et0614/e-sensor/firmware/E_Sensor_Main.X/main.c

#include "mcc_generated_files/system/system.h"
#include "mcc_generated_files/system/ccp.h"
#include "mcc_generated_files/timer/tca0.h"
#include "mcc_generated_files/system/pins.h"

#include <avr/interrupt.h>
#include <avr/wdt.h>
#include <avr/sleep.h>

#include "tinyusb/tusb.h"
#include "midi_app.h"
#include "opt3001.h"
#include "velocity_sensor.h"
#include "stcc4.h"
#include "eeprom_manager.h"

#include <util/atomic.h>

volatile uint32_t system_millis = 0;
volatile uint32_t sec_timer = 0;
// CO2 初期調整用のタイマ。休眠状態は -1、調整要求受信時に 0 にセットされ、
// ISR が 0 以上の場合のみ 1msec 刻みでインクリメントする。起動直後に
// CMD_CONDITIONING_DONE が誤発火しないよう -1 で初期化する。
volatile int32_t co2_pfm_timer = -1;

volatile bool conditioning_requested = false;

// 1msecごとのコールバック関数
void msecHandler(void)
{
    // ISR内なので他割り込みによる競合は無い。単純インクリメントでよい。
    system_millis++;
    sec_timer++;
    if(0 <= co2_pfm_timer) co2_pfm_timer++;
}

// 32bit変数をアトミックに読むヘルパ
static inline uint32_t atomic_load_u32(volatile uint32_t *p) {
    uint32_t v;
    ATOMIC_BLOCK(ATOMIC_RESTORESTATE) { v = *p; }
    return v;
}
static inline int32_t atomic_load_i32(volatile int32_t *p) {
    int32_t v;
    ATOMIC_BLOCK(ATOMIC_RESTORESTATE) { v = *p; }
    return v;
}
static inline void atomic_store_u32(volatile uint32_t *p, uint32_t v) {
    ATOMIC_BLOCK(ATOMIC_RESTORESTATE) { *p = v; }
}
static inline void atomic_store_i32(volatile int32_t *p, int32_t v) {
    ATOMIC_BLOCK(ATOMIC_RESTORESTATE) { *p = v; }
}

// TinyUSBが参照する時間取得関数をオーバーライド
uint32_t tusb_time_millis_api(void) {
    uint32_t now;
    ATOMIC_BLOCK(ATOMIC_RESTORESTATE) {
        now = system_millis;
    }
    return now;
}

void setup_usb(void) {
    // 1. 周波数を 12MHz に設定 (USB FS の下限。Microchip 公式 CDC 例より、AVR DU の
    //    USB フルスピード動作に必要な最低オシレータ周波数は 12MHz。24MHz から半減させ、
    //    発振器・常時動作周辺（USB/TCA0/I2C）の動的消費＝自己発熱を更に低減する。
    //    ※USB の下限が 12MHz なので、USB 接続中はこれ以上は下げられない。
    // 2. AUTOTUNE を SOF (USB Start of Frame) に同期する設定にする（12MHz でも SOF 同期は有効）
    ccp_write_io((void *)&(CLKCTRL.OSCHFCTRLA), CLKCTRL_FRQSEL_12M_gc | CLKCTRL_AUTOTUNE_SOF_gc);
    
    SYSCFG.VUSBCTRL = SYSCFG_USBVREG_bm;
    
     //Tiny USB初期化
     tusb_init();
     
     // PCに対してUSB接続を通知
    USB0.CTRLB |= USB_ATTACH_bm;
}

int main(void)
{
    SYSTEM_Initialize();

    // EEPROM読み込み
    EM_loadEEPROM();
    
    // センサ初期化
    STCC4_initialize();
    OPT3001_Initialize();
    VELS_stop(); // 起動時は風速計OFF（5V遮断）を明示。On はホストからの指令で行う
    
    // STCC4は初回起動時のみ工場出荷状態に初期化
    if(EM_Is_First_Run)
    {
        if(STCC4_performFactoryReset())
        {
            //成功したらフラグ解除。失敗の場合は次回起動時に持ち越す
            EM_Is_First_Run = false;
            EM_updateEEPROM();
        }
    }
    STCC4_exitSleep();
    STCC4_startContinuousMeasurement(); //CO2連続計測開始
    
    MIDI_APP_Initialize();
    
    // イベントハンドラ登録
    TCA0_OverflowCallbackRegister(msecHandler); // 1msecタイマ
    
    // USB通信用意
    setup_usb();

    // 割り込み開始
    sei();

    B_LED_SetLow();

    // スリープモードは IDLE。CPU コアのみ停止し、USB・TCA0(1ms)・I2C 等の周辺は
    // 動作を継続する。割込（USB 転送/SOF、1ms タイマ等）で即復帰してループを回す。
    // これにより常時クロックでビジーループしていた分の動的消費（=自己発熱）を抑える。
    // ※STANDBY/POWER-DOWN は USB クロックも停止し接続が切れるため使用不可。
    set_sleep_mode(SLEEP_MODE_IDLE);

    while(1)
    {
        // ウォッチドッグキック
        wdt_reset();

        tud_task();         // USBスタック
        MIDI_APP_Tasks();   // MIDIアプリ処理

        // CO2センサ初期調整関連
        if(conditioning_requested && STCC4_performConditioning())
        {
            conditioning_requested = false;
            MIDI_SendSysEx(CMD_CONDITIONING_START, NULL, 0);
            atomic_store_i32(&co2_pfm_timer, 0);
        }
        // 初期調整（約22sec）が終わったらCO2センサの連続計測開始
        if(23000 < atomic_load_i32(&co2_pfm_timer))
        {
            if(STCC4_startContinuousMeasurement())
            {
                MIDI_SendSysEx(CMD_CONDITIONING_DONE, NULL, 0);
                atomic_store_i32(&co2_pfm_timer, -1);
            }
            else
            {
                // 失敗時は I2C を叩き続けないよう 1sec バックオフして再試行
                atomic_store_i32(&co2_pfm_timer, 22000);
            }
        }

        // 1secタイマ
        if(1000 < atomic_load_u32(&sec_timer))
        {
            atomic_store_u32(&sec_timer, 0);

            if(EM_Sensing_Enabled) B_LED_Toggle();
            else B_LED_SetLow();
        }

        // 次の割込まで CPU を休止（IDLE）。USB 割込・1ms タイマ等で復帰する。
        // 遅くとも 1ms ごとに TCA0 で起床するため処理の取りこぼしは生じない。
        sleep_mode();
    }
}
