et0614/e-sensor/firmware/E_Sensor_Main.X/midi_app.c

#include "midi_app.h"
#include "sensor_data.h"
#include "crc.h"
#include "tinyusb/tusb.h"

#include <string.h>
#include <util/atomic.h>

#include "opt3001.h"
#include "stcc4.h"
#include "velocity_sensor.h"
//#include "smAverage.h" //平均化ユーティリティ
#include "serial.h"
#include "eeprom_manager.h"

// バージョン
#define VERSION_MAJOR (1)
#define VERSION_MINOR (1)
#define VERSION_REVISION (2)

// 計測時間間隔 [msec]
#define MEAS_CO2_SPAN (1000)
#define MEAS_ILL_SPAN (800)
#define MEAS_VEL_SPAN (200)

#define SYSEX_BUF_SIZE 64
static uint8_t rx_buf[SYSEX_BUF_SIZE];
static uint16_t rx_idx = 0;

// SysEx受信の状態機械
typedef enum {
    SYSEX_IDLE,      // 0xF0 待ち
    SYSEX_RX,        // ペイロード蓄積中
    SYSEX_OVERFLOW   // バッファ溢れ: 0xF7 までデータを破棄
} sysex_rx_state_t;

static sysex_rx_state_t rx_state = SYSEX_IDLE;

static inline void sysex_reset_rx(void) {
    rx_idx = 0;
    rx_state = SYSEX_IDLE;
}

// 時間経過[msec]（main.cから参照）
extern volatile uint32_t system_millis;

// 最終計測時間
static uint32_t last_meas_co2 = 0;
static uint32_t last_meas_vel = 0;
static uint32_t last_meas_ill = 0;

// 現在の計測値
static volatile SensorData_t current_data;

// 風速センサ有効フラグ。起動時は OFF（main.c の VELS_stop() で enable=0 を送信）。
// 5V回路の入切は Velocity MCU 側の PD3(→TPS22965) が enable レジスタに従って行う。
// OFF 中は風速回路が無給電で計測値が無い（読んでも 0/旧値）ため、VELS_readMeasurement
// を発行せず status bit2 を落とす。On はホストからの CMD_START_VEL で開始する。
static bool velocity_enabled = false;

// CO2センサの初期調整要求フラグ
extern volatile bool conditioning_requested;

//static SmAverage smaCO2; // 60秒平均を計算するインスタンス

// <editor-fold defaultstate="collapsed" desc="内部関数">

// 風速補正係数 (float) の健全性チェック。
// NaN / Inf / 想定外に巨大な値を弾き、EEPROM 側に破壊的な値が永続化されるのを防ぐ。
// 明らかな「ゴミ」を弾く程度の緩いレンジチェック。
static bool is_valid_coef_array(const float *c, uint8_t n) {
    for (uint8_t i = 0; i < n; i++) {
        // NaN は自己比較が false になる性質で検出
        if (c[i] != c[i]) return false;
        // ±Inf および桁数として非現実的な値を弾く
        if (c[i] > 1.0e30f || c[i] < -1.0e30f) return false;
    }
    return true;
}

// Host (Python) から受信した係数バイト列はビッグエンディアンだが、Main MCU
// (AVR) はリトルエンディアン。is_valid_coef_array は float として解釈して
// レンジチェックを行うため、検証前に byte swap して LE 解釈と一致させる。
// Velocity MCU 側は受信した BE バイトをそのまま保存し読出時に swap して
// 計算するため、I2C 送信は元の BE バイトを使うこと。
static inline void swap_float_bytes(float* f) {
    uint8_t* p = (uint8_t*)f;
    uint8_t t;
    t = p[0]; p[0] = p[3]; p[3] = t;
    t = p[1]; p[1] = p[2]; p[2] = t;
}

// 4bitニブル分割してパケット送信
static void send_nibbles(uint8_t val, uint8_t* buffer, uint8_t* buf_idx) {
    uint8_t nibbles[2] = { (val >> 4) & 0x0F, val & 0x0F };
    for (uint8_t i = 0; i < 2; i++) {
        buffer[(*buf_idx)++] = nibbles[i];
        if (*buf_idx == 3) {
            uint8_t packet[4] = { 0x04, buffer[0], buffer[1], buffer[2] };
            tud_midi_packet_write(packet);
            *buf_idx = 0;
        }
    }
}

// ニブルをバイトに復元する内部関数
static void decode_and_process_sysex(uint8_t* encoded_data, uint16_t len) {
    uint8_t decoded[SYSEX_BUF_SIZE / 2];
    uint16_t d_idx = 0;

    // 最低限の長さ確認 (ManufacturerID + CommandID)
    if (len < 2) return;
    // ペイロードはニブル対で構成されるため、残りバイト数は偶数でなければ不正
    if (((len - 2) % 2) != 0) return;

    // 最初の2バイトは Manufacturer ID (7D) と Command ID なのでスキップせず解析
    uint8_t manufacturer_id = encoded_data[0];
    uint8_t command_id = encoded_data[1];

    if (manufacturer_id != SYSEX_MANUFACTURER_ID) return;

    // 3バイト目以降がニブル分割されたデータ本体
    for (uint16_t i = 2; i + 1 < len && d_idx < sizeof(decoded); i += 2) {
        decoded[d_idx++] = (encoded_data[i] << 4) | encoded_data[i+1];
    }

    // コマンド分岐**********************
    float coef_tmp[5];

    switch (command_id) {
        case CMD_REQ_DATA:
            MIDI_SendSysEx(CMD_REPORT_DATA, (uint8_t*)&current_data, sizeof(SensorData_t));
            break;
        
        case CMD_START_MEAS: // 計測開始命令（以降、Host から CMD_REQ_DATA を受けた時のみ応答）
            EM_Sensing_Enabled = true;
            EM_updateEEPROM();
            break;

        case CMD_STOP_MEAS: //計測停止命令
            EM_Sensing_Enabled = false;
            EM_updateEEPROM();
            break;

        case CMD_COEF_A_DATA: // 係数A受信
            if (d_idx >= 21 && CRC_calc8(decoded, 20) == decoded[20]) {
                // 型パニング回避: uint8_t 配列から float 配列へ memcpy で転送
                memcpy(coef_tmp, decoded, 20);
                // 検証用に byte swap した複製を作る (受信は BE, 検証は LE 解釈で行う)
                float validation_tmp[5];
                memcpy(validation_tmp, coef_tmp, 20);
                for (uint8_t i = 0; i < 5; i++) swap_float_bytes(&validation_tmp[i]);
                if (is_valid_coef_array(validation_tmp, 5))
                    VELS_writeCoefficients(coef_tmp, true); // I2C には BE のまま送る
            }
            break;

        case CMD_REQ_COEF_A: // 係数A要求
            if (VELS_readCoefficients(coef_tmp, true))
                MIDI_SendSysEx(CMD_COEF_A_DATA, (uint8_t*)coef_tmp, 20);
            break;

        case CMD_COEF_B_DATA: // 係数B受信
            if (d_idx >= 21 && CRC_calc8(decoded, 20) == decoded[20]) {
                memcpy(coef_tmp, decoded, 20);
                // 検証用に byte swap した複製を作る (受信は BE, 検証は LE 解釈で行う)
                float validation_tmp[5];
                memcpy(validation_tmp, coef_tmp, 20);
                for (uint8_t i = 0; i < 5; i++) swap_float_bytes(&validation_tmp[i]);
                if (is_valid_coef_array(validation_tmp, 5))
                    VELS_writeCoefficients(coef_tmp, false); // I2C には BE のまま送る
            }
            break;

        case CMD_REQ_COEF_B: // 係数B要求
            if (VELS_readCoefficients(coef_tmp, false))
                MIDI_SendSysEx(CMD_COEF_B_DATA, (uint8_t*)coef_tmp, 20);
            break;
            
        case CMD_REQ_ID: // シリアル番号送信要求
            {
                uint32_t hash = SERIAL_get_serial_hash();                
                // 4バイトのバイナリデータとしてパケット準備
                uint8_t hash_bytes[4];
                hash_bytes[0] = (uint8_t)(hash >> 24);
                hash_bytes[1] = (uint8_t)(hash >> 16);
                hash_bytes[2] = (uint8_t)(hash >> 8);
                hash_bytes[3] = (uint8_t)(hash);
                MIDI_SendSysEx(CMD_ID_DATA, hash_bytes, 4);
            }
            break;
            
        case CMD_REQ_VERSION: // Version送信要求
            {
                uint8_t version[3] = { VERSION_MAJOR, VERSION_MINOR, VERSION_REVISION };
                MIDI_SendSysEx(CMD_VERSION_DATA, version, 3);
            }
            break;
            
        case CMD_REQ_CO2_CALIB: // CO2校正要求
            {
                if (d_idx >= 3 && CRC_calc8(decoded, 2) == decoded[2]) {
                    uint16_t co2lvl = (decoded[0] << 8) | decoded[1];
                    // 補正値（差分）は符号付き 16bit。失敗時は -1 (0xFFFF) が入る。
                    int16_t corct = 0;
                    if (STCC4_performForcedRecalibration(co2lvl, &corct)) {
                        uint16_t corct_u = (uint16_t)corct;
                        uint8_t corct_bytes[2] = {
                            (uint8_t)(corct_u >> 8),
                            (uint8_t)(corct_u & 0xFF)
                        };
                        MIDI_SendSysEx(CMD_CO2_CALIB_RESULT, corct_bytes, 2);
                    }
                }
            }
            break;
            
        case CMD_REQ_CO2_FACTORY_RESET: // CO2センサの工場出荷時初期化要求
            if(STCC4_performFactoryReset())
                MIDI_SendSysEx(CMD_CO2_FACTORY_RESET_DONE, NULL, 0);
            break;
            
        case CMD_REQ_CONDITIONING: // CO2初期調整要求
            conditioning_requested = true;
            break;

        case CMD_START_VEL: // 風速センサ起動
            // I2C で enable=1 を送信。Velocity MCU が PD3(→TPS22965 ON, Active High)を
            // High にして風速回路へ 5V を供給し、予熱を経て計測を再開する。
            // (PWR_DOWN 中の Velocity MCU は TWI アドレス一致で起床して受信する)
            VELS_start();
            velocity_enabled = true;
            break;

        case CMD_STOP_VEL: // 風速センサ停止
            // I2C で enable=0 を送信。Velocity MCU が PD3 を Low にして 5V を遮断し
            // (自己発熱を停止)、PWR_DOWN へ移行する。先に停止指令を送ってから
            // ポーリングを止める(以降は応答しないため readMeasurement を発行しない)。
            VELS_stop();
            velocity_enabled = false;
            // 停止直後に古い読値が画面に残らないよう、計測値を 0 にしフラグを落とす
            current_data.velocity = 0;
            current_data.voltage  = 0;
            current_data.status &= ~(1 << 2);
            break;
    }
}

// </editor-fold>

// <editor-fold defaultstate="collapsed" desc="公開関数">

void MIDI_APP_Initialize(void)
{
    //SMA_Init(&smaCO2); //CO2センサ平均化インスタンスの初期化
}

// 汎用SysEx送信関数
void MIDI_SendSysEx(uint8_t command_id, uint8_t* data, uint16_t len) {
    if (!tud_midi_mounted()) return;

    uint8_t buffer[3];
    uint8_t buf_idx = 0;
    uint8_t crc = CRC_calc8(data, (uint8_t)len);

    // Header: F0, 7D, CommandID
    uint8_t head[4] = { 0x04, 0xF0, 0x7D, command_id };
    tud_midi_packet_write(head);

    // Data + CRC
    for (uint16_t i = 0; i <= len; i++) {
        send_nibbles((i < len) ? data[i] : crc, buffer, &buf_idx);
    }

    // Footer: F7
    buffer[buf_idx++] = 0xF7;
    uint8_t cin = (buf_idx == 1) ? 0x05 : (buf_idx == 2) ? 0x06 : 0x07;
    uint8_t footer[4] = { cin, buffer[0], (buf_idx > 1 ? buffer[1] : 0), (buf_idx > 2 ? buffer[2] : 0) };
    tud_midi_packet_write(footer);
}

uint32_t get_system_millis(){
    uint32_t now;
    ATOMIC_BLOCK(ATOMIC_RESTORESTATE) {
        now = system_millis;
    }
    return now;
}

// 受信バイトを状態機械に1バイト供給する。
// パケット本体バイトのみを渡す想定（0xF0 で開始、0xF7 で終了）。
static void sysex_feed_byte(uint8_t b) {
    if (b == 0xF0) {
        // 開始バイト: 既存状態を破棄して再同期
        rx_idx = 0;
        rx_state = SYSEX_RX;
        return;
    }
    if (b == 0xF7) {
        // 終了バイト: RX 中なら解析、Overflow/IDLE なら破棄
        if (rx_state == SYSEX_RX) {
            decode_and_process_sysex(rx_buf, rx_idx);
        }
        sysex_reset_rx();
        return;
    }
    // その他のステータスバイト (>= 0x80) は SysEx 中なら中断して破棄
    if (b & 0x80) {
        sysex_reset_rx();
        return;
    }
    // データバイト (< 0x80)
    if (rx_state == SYSEX_RX) {
        if (rx_idx < SYSEX_BUF_SIZE) {
            rx_buf[rx_idx++] = b;
        } else {
            // バッファ溢れ: 以降のデータは捨てて 0xF7 待ちに遷移
            rx_state = SYSEX_OVERFLOW;
        }
    }
    // IDLE / OVERFLOW のデータバイトは黙って破棄
}

void MIDI_APP_Tasks(void) {
    // 受信処理
    if (tud_midi_available()) {
        uint8_t packet[4];
        while (tud_midi_packet_read(packet)) {
            uint8_t cin = packet[0] & 0x0F; // CINを取得

            // CINごとの応答
            switch (cin) {
                case 0x04: // SysEx 開始 または 継続 (3バイト)
                    sysex_feed_byte(packet[1]);
                    sysex_feed_byte(packet[2]);
                    sysex_feed_byte(packet[3]);
                    break;

                case 0x05: // SysEx 終了 (1バイト: F7 のみ、または単一バイトメッセージ)
                    sysex_feed_byte(packet[1]);
                    break;

                case 0x06: // SysEx 終了 (2バイト)
                    sysex_feed_byte(packet[1]);
                    sysex_feed_byte(packet[2]);
                    break;

                case 0x07: // SysEx 終了 (3バイト)
                    sysex_feed_byte(packet[1]);
                    sysex_feed_byte(packet[2]);
                    sysex_feed_byte(packet[3]);
                    break;

                case 0x08: // ノートOff
                    break; // スルー

                case 0x09: // ノートOn
                    break; // スルー

                case 0x0B: // Control Change
                    break; // スルー

                default:
                    // その他のメッセージはスルー
                    break;
            }
        }
    }
    
    // 計測処理 (計測中のみ)
    if (EM_Sensing_Enabled) {
        
        // 照度
        if (MEAS_ILL_SPAN <= get_system_millis() - last_meas_ill)
        {
            float ill_d;
            if(OPT3001_ReadALS(&ill_d))
            { 
                current_data.illuminance = (uint32_t)(10 * ill_d);
                current_data.status |= (1 << 0);
                
                last_meas_ill = get_system_millis();
            }
            else
            {
                current_data.status &= ~(1 << 0); // 計測失敗
                last_meas_ill += 10; // 10msec休んで再トライ
            }
        }
        
        // CO2, 温度, 湿度
        if (MEAS_CO2_SPAN <= get_system_millis() - last_meas_co2)
        {
            uint16_t co2_u = 0;
            float tmp_f = 0;
            float hmd_f = 0;
            if(STCC4_readMeasurement(&co2_u, &tmp_f, &hmd_f))
            {
                //SMA_Add(&smaCO2, co2_u);
                //uint16_t co2Ave = SMA_GetAverage(&smaCO2);
                //current_data.co2_ppm = co2Ave;
                current_data.co2_ppm = co2_u;
                current_data.temperature = (int16_t)(100 * tmp_f);
                current_data.humidity = (uint16_t)(100 * hmd_f);
                current_data.status |= (1 << 1);
                
                last_meas_co2 = get_system_millis();
            }
            else
            {
                current_data.status &= ~(1 << 1); // 計測失敗
                last_meas_co2 += 50; // 50msec休んで再トライ
            }
        }
        
        // 風速。停止中は I2C を発行しない（Velocity MCU は PWR_DOWN で応答できず、
        // 失敗扱いになるだけでなく I2C タイムアウトでメインループが詰まる）。
        if (!velocity_enabled)
        {
            last_meas_vel = get_system_millis();
        }
        else if (MEAS_VEL_SPAN <= get_system_millis() - last_meas_vel)
        {
            uint16_t velocity;
            uint16_t voltage;
            if(VELS_readMeasurement(&velocity, &voltage))
            {
                current_data.velocity = velocity;
                current_data.voltage = voltage;
                current_data.status |= (1 << 2);

                last_meas_vel = get_system_millis();
            }
            else
            {
                current_data.status &= ~(1 << 2); // 計測失敗
                last_meas_vel += 10; // 10msec休んで再トライ
            }
        }
    }
}

// </editor-fold>
